somhi/DECA_retro_cape_2/datasheets-references/LDO/ams1117_sch_R1_3.3ohm.jpeg

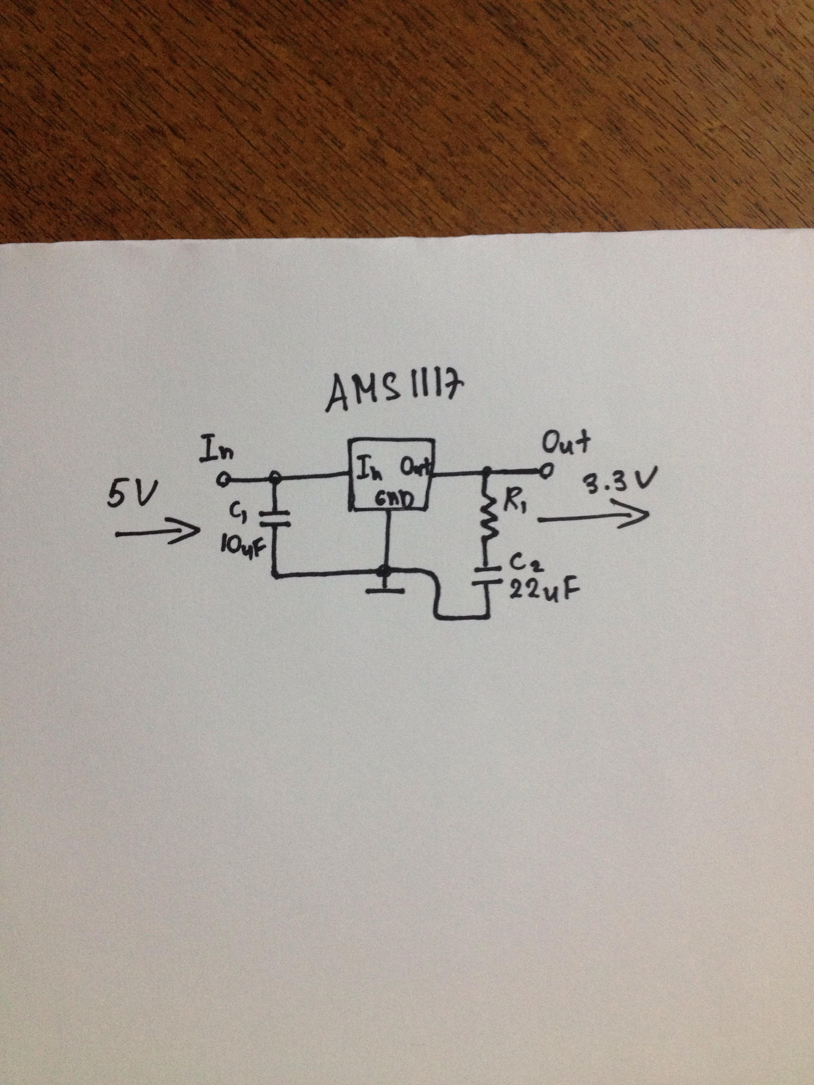
datasheets-references/LDO/ams1117_sch_R1_3.3ohm.jpeg
