somhi/DECA_retro_cape_2/datasheets-references/LDO/bad-footprint/ldo_2v5_rework.jpg

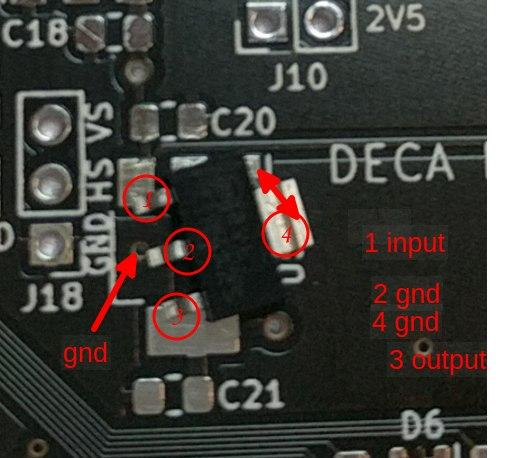
datasheets-references/LDO/bad-footprint/ldo_2v5_rework.jpg
