somhi/DECA_retro_cape_2/datasheets-references/REF_circuits_connectors/db9_others.jpg

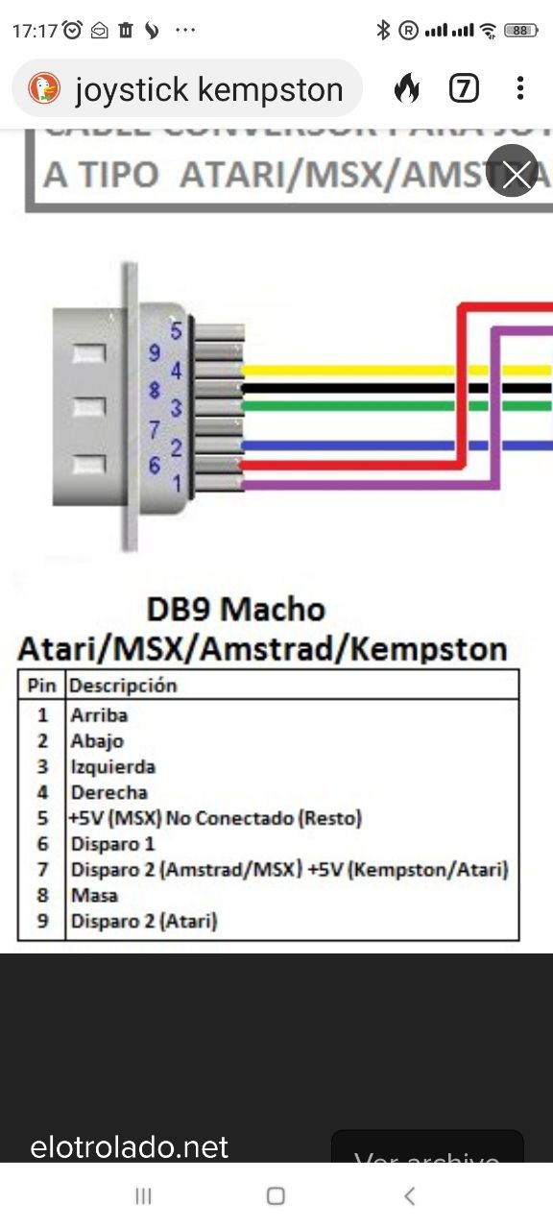
datasheets-references/REF_circuits_connectors/db9_others.jpg
