somhi/DECA_retro_cape_2/datasheets-references/REF_circuits_connectors/DE10-Nano-mides.jpg

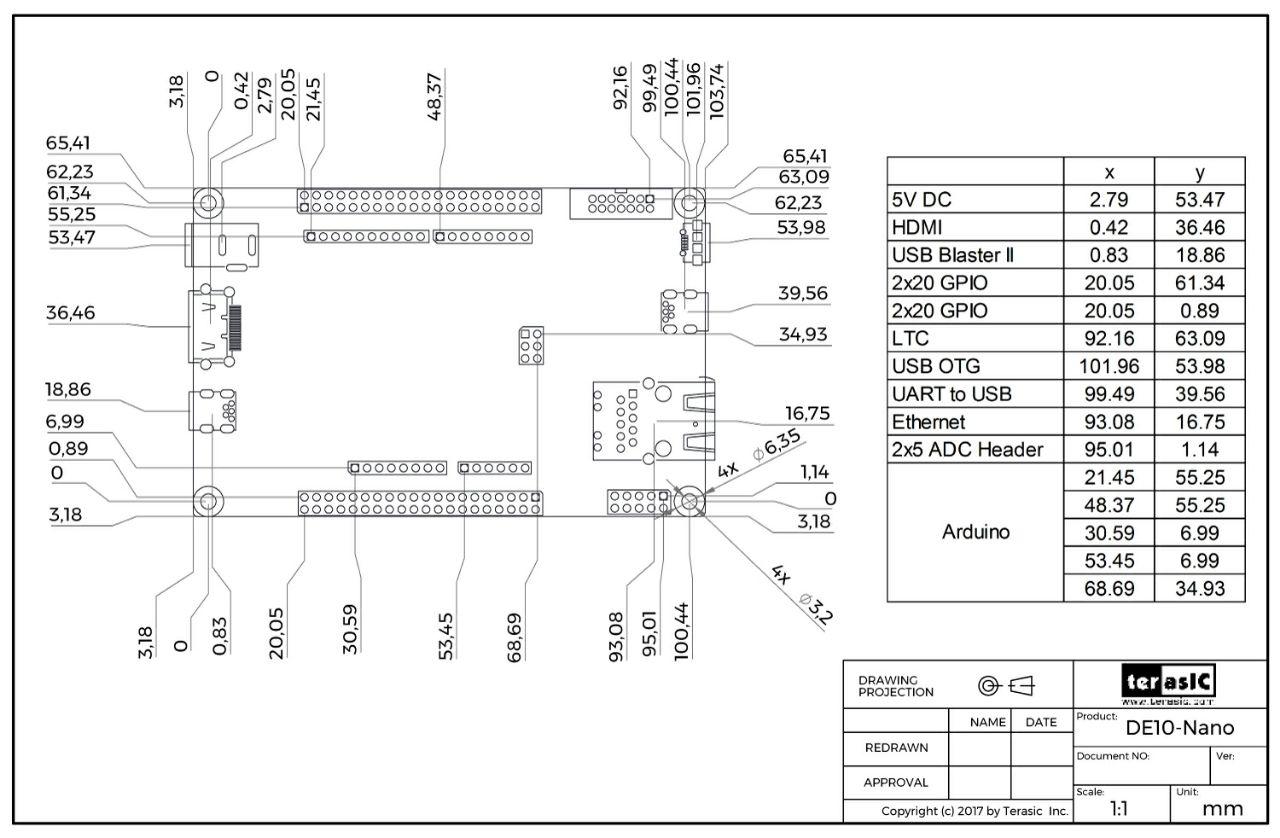
datasheets-references/REF_circuits_connectors/DE10-Nano-mides.jpg
