somhi/DECA_retro_cape_2/datasheets-references/REF_circuits_connectors/pmod-vga-serigrafia-ok.jpg

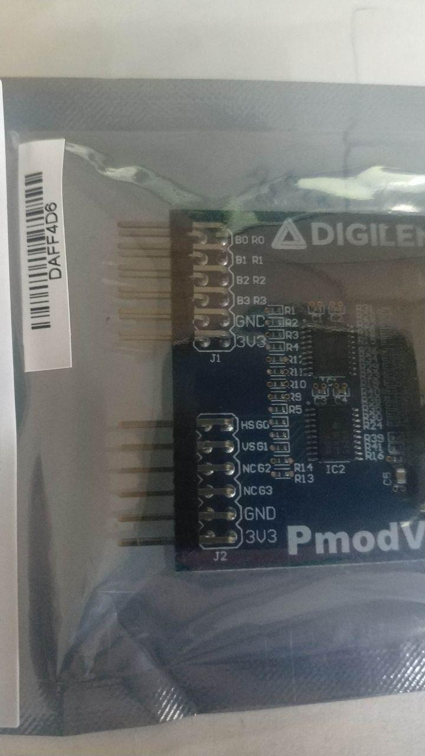
datasheets-references/REF_circuits_connectors/pmod-vga-serigrafia-ok.jpg
