somhi/DECA_retro_cape_2/datasheets-references/REF_circuits_connectors/USERIO.png

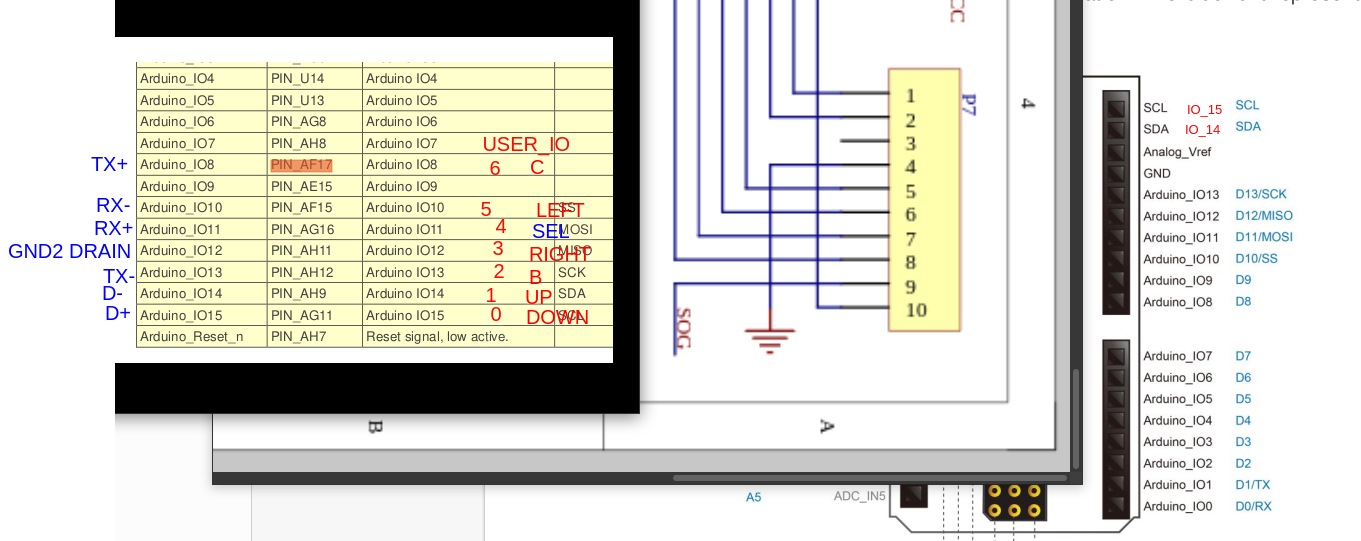
datasheets-references/REF_circuits_connectors/USERIO.png
