somhi/DECA_retro_cape_2/datasheets-references/Ref_joy/c96-FXLP34P5XCT-ND.jpg

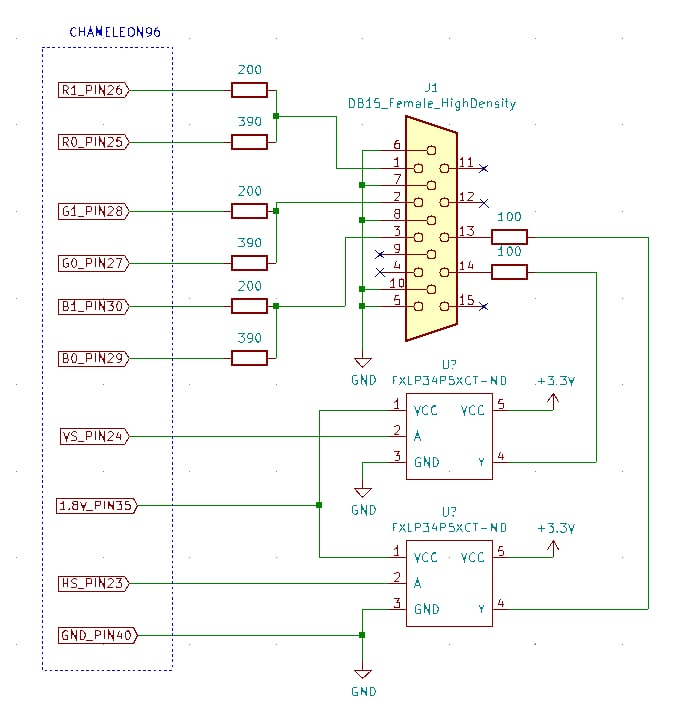
datasheets-references/Ref_joy/c96-FXLP34P5XCT-ND.jpg
