somhi/DECA_retro_cape_2/datasheets-references/Ref_joy/papilio-shield.png

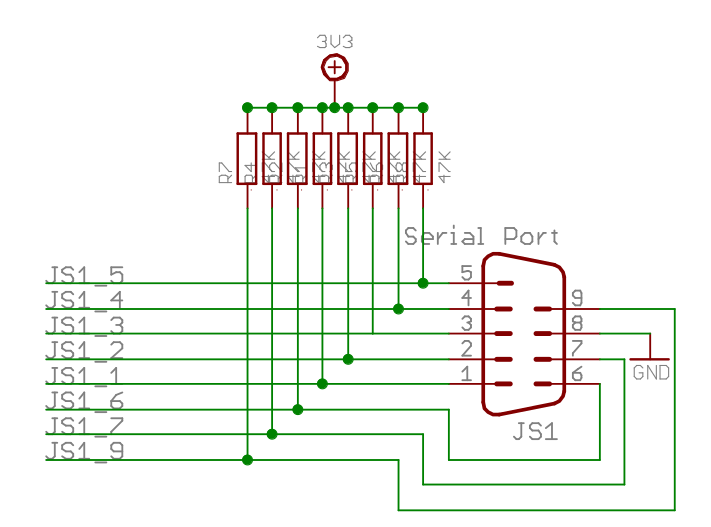
datasheets-references/Ref_joy/papilio-shield.png
