somhi/DECA_retro_cape_2/datasheets-references/Ref_joy/qmtech_minimig.png

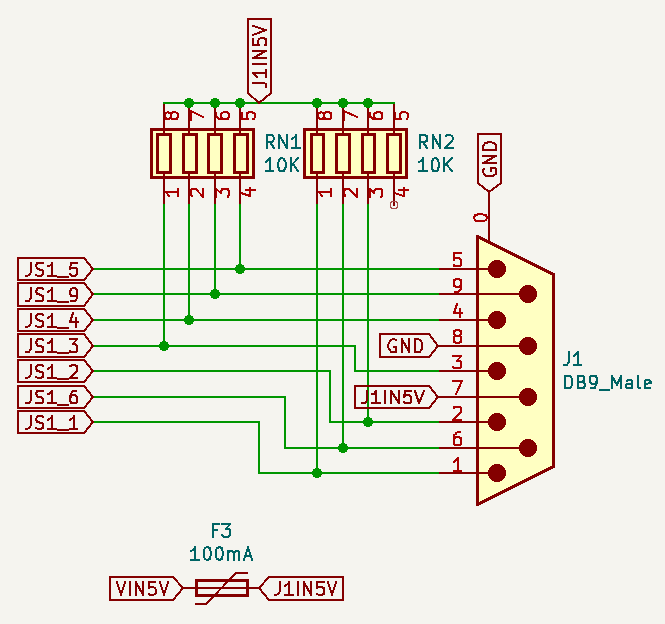
datasheets-references/Ref_joy/qmtech_minimig.png
