somhi/DECA_retro_cape_2/datasheets-references/Ref_joy/Tom_verbeure.png

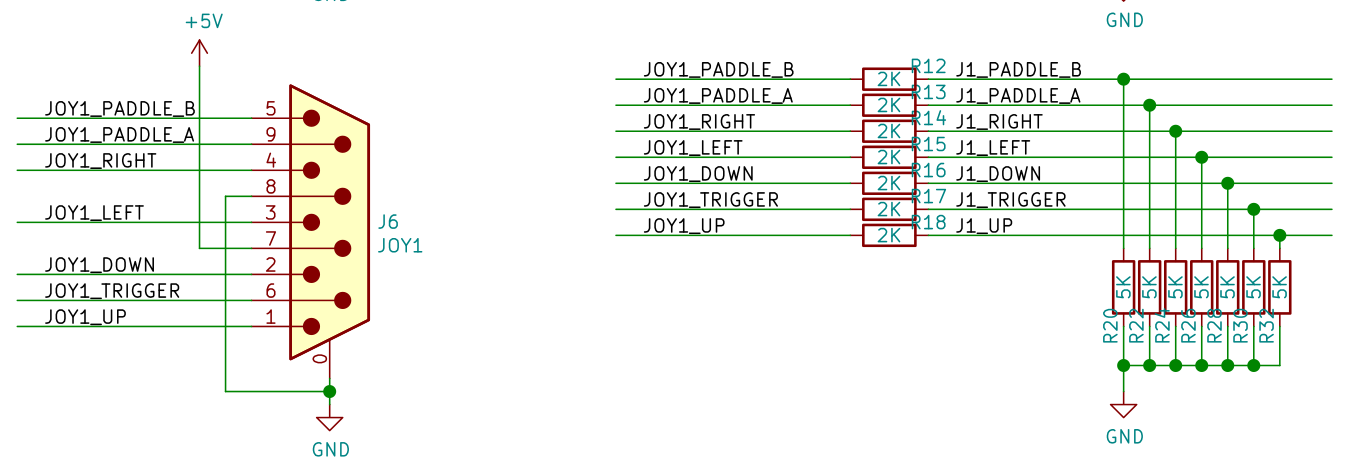
datasheets-references/Ref_joy/Tom_verbeure.png
