somhi/DECA_retro_cape_2/datasheets-references/Ref_ps2/Atlas_ps2_2_usb.png

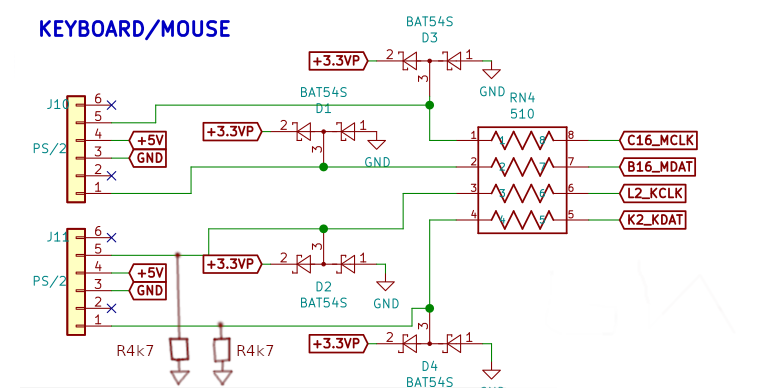
datasheets-references/Ref_ps2/Atlas_ps2_2_usb.png
