somhi/DECA_retro_cape_2/datasheets-references/Ref_ps2/DE1.png

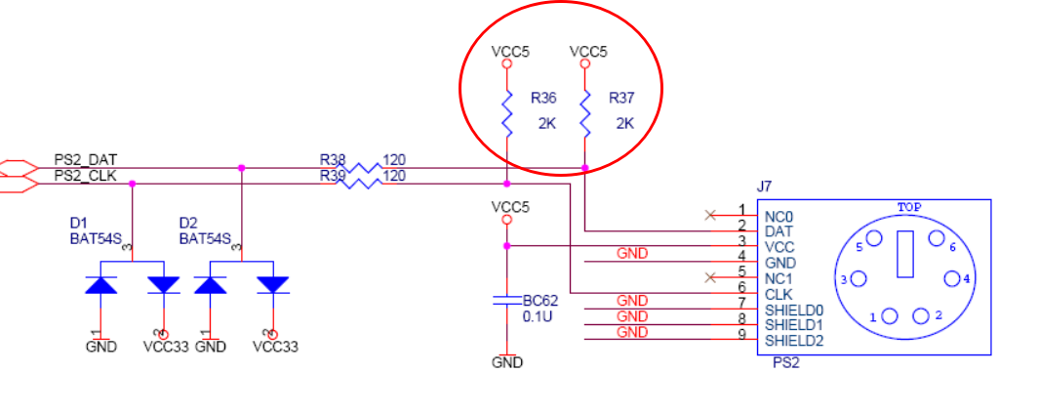
datasheets-references/Ref_ps2/DE1.png
