somhi/DECA_retro_cape_2/datasheets-references/Ref_ps2/ksnip_20220512-234157.png

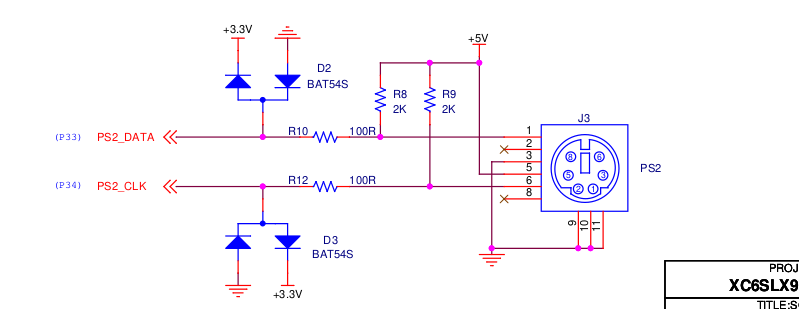
datasheets-references/Ref_ps2/ksnip_20220512-234157.png
