somhi/DECA_retro_cape_2/datasheets-references/Ref_ps2/ksnip_20220516-202812.png

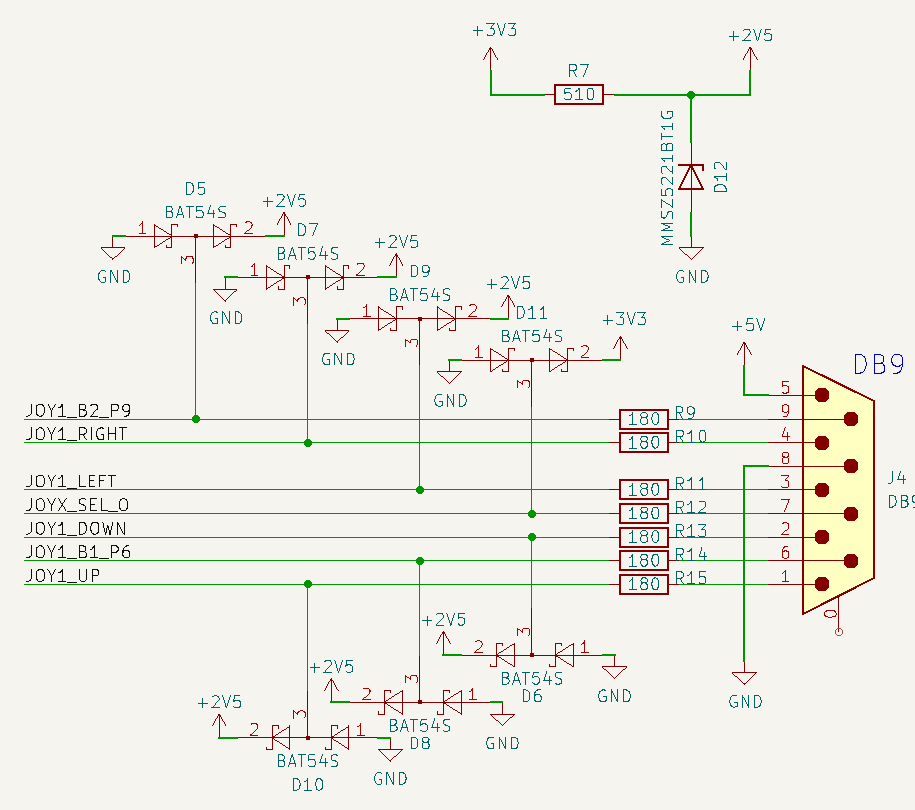
datasheets-references/Ref_ps2/ksnip_20220516-202812.png
