somhi/DECA_retro_cape_2/datasheets-references/Shift_level/level_shift_other/BSS138.jpg

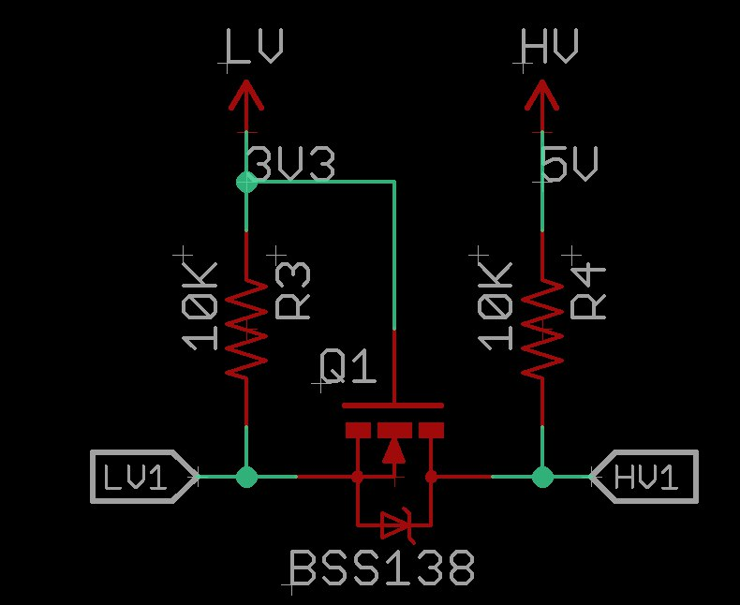
datasheets-references/Shift_level/level_shift_other/BSS138.jpg
