somhi/DECA_retro_cape_2/jlcpcb/capture-2022-12-25T13_55_34.772Z.png

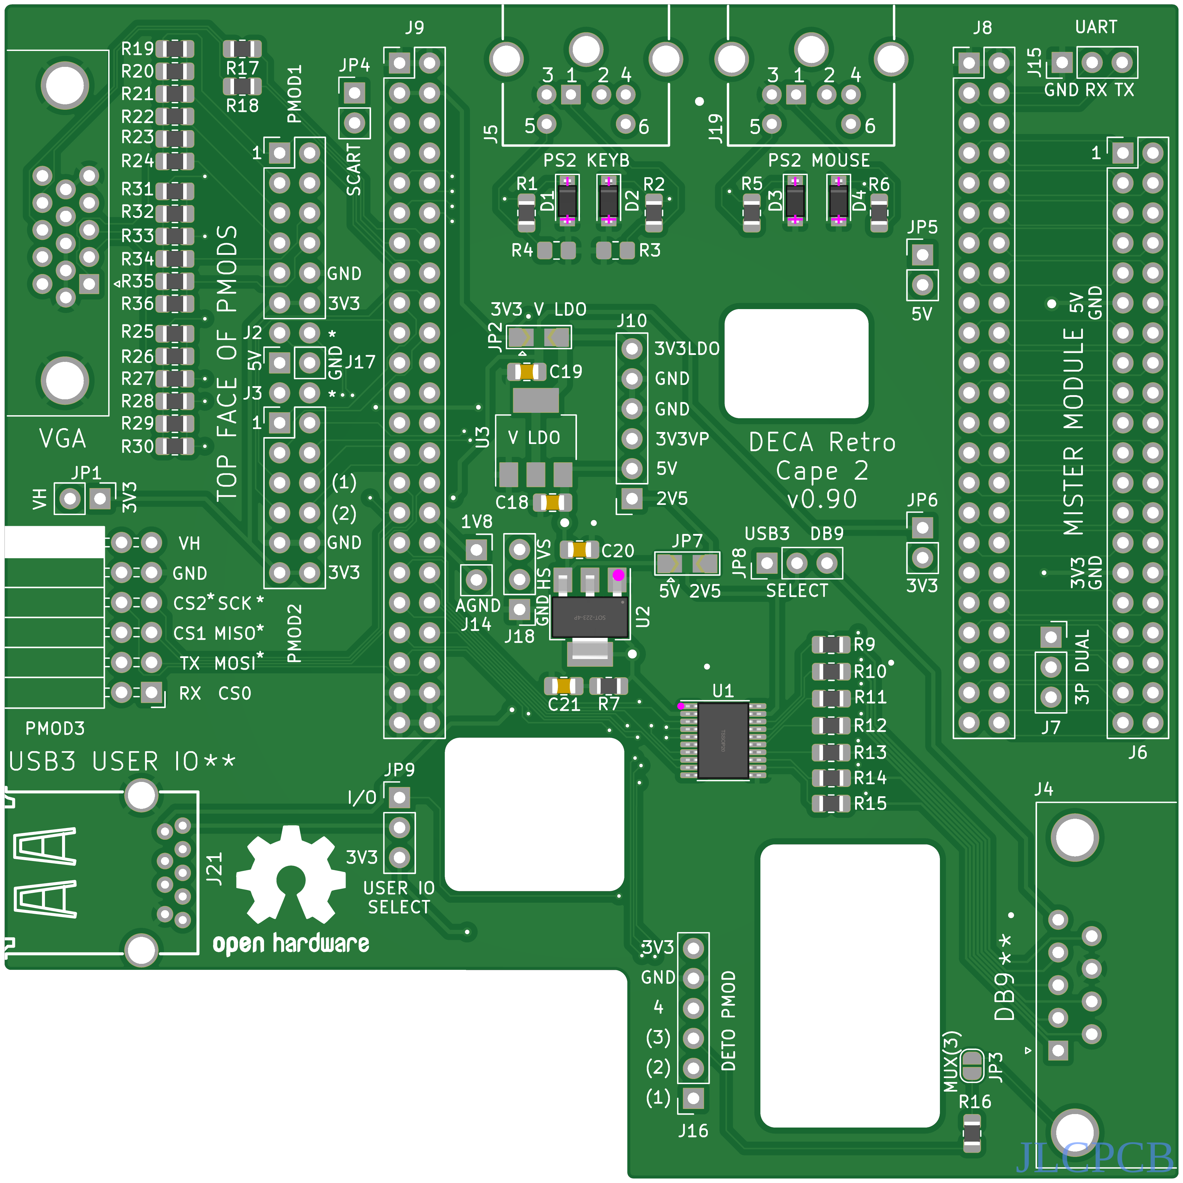
jlcpcb/capture-2022-12-25T13_55_34.772Z.png
